floxcap/fly2040/pcb/usb_programmer/3DSteps/2-84952-4.step

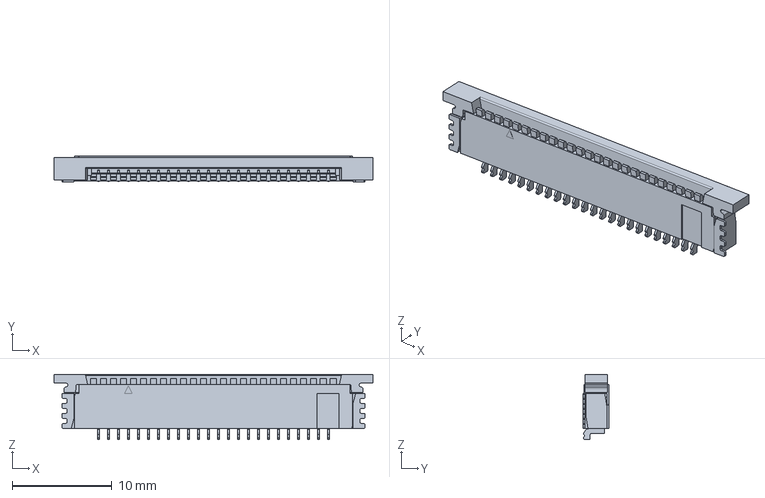
[picture p23: CAD file, 2023-07-07]
pcb/usb_programmer/3DSteps/2-84952-4.step
31.9 x 2.56 x 6.54 mm
