floxcap/fly2040/pcb/usb_programmer/3DSteps/S2B-PH-SM4-TB(LF)(SN)--3DModel-STEP-56544.STEP

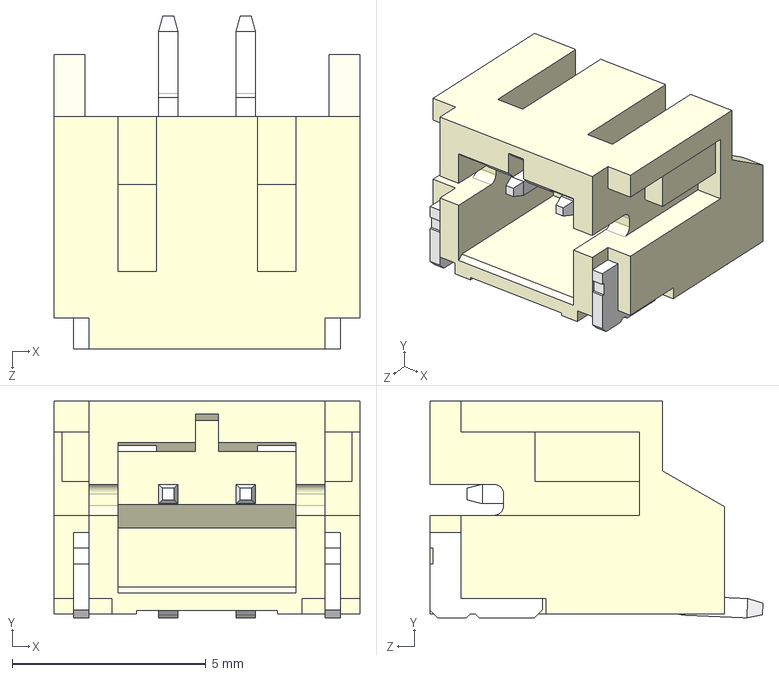
[picture p24: CAD file, 2023-07-07]
pcb/usb_programmer/3DSteps/S2B-PH-SM4-TB(LF)(SN)--3DModel-STEP-56544.STEP
7.90 x 5.60 x 8.60 mm
