floxcap/fly2040/pcb/usb_programmer/3DSteps/KMR621NG LFS.step

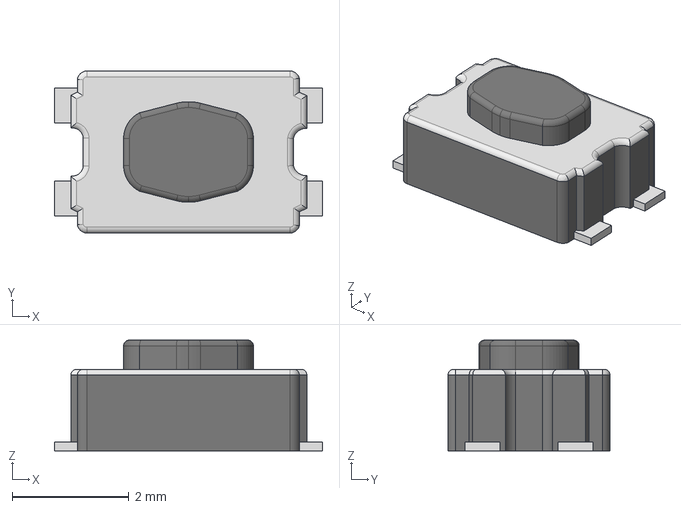
[picture p25: CAD file, 2023-07-07]
pcb/usb_programmer/3DSteps/KMR621NG LFS.step
4.60 x 2.78 x 1.90 mm
