floxcap/fly2040/pcb/usb_programmer/3DSteps/WLCSP6_1P48X0P98_ONS.step

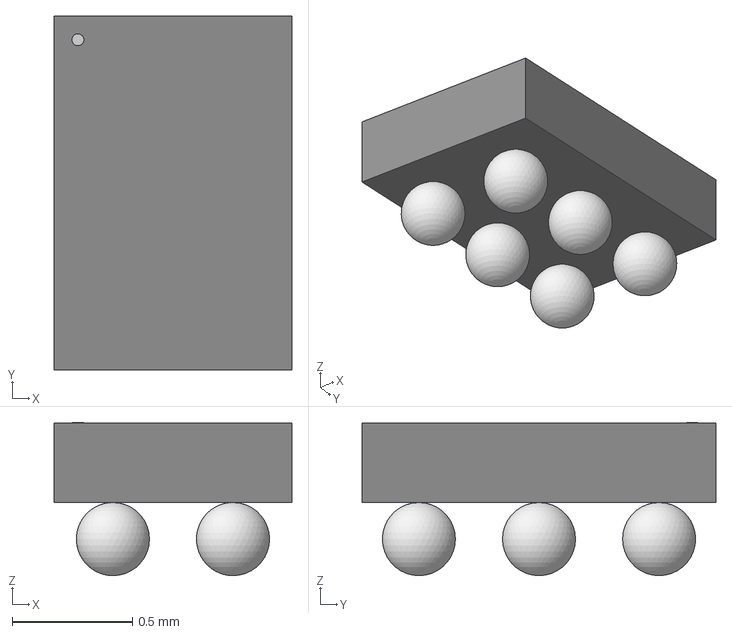
[picture p26: CAD file, 2023-07-07]
pcb/usb_programmer/3DSteps/WLCSP6_1P48X0P98_ONS.step
0.99 x 1.47 x 0.638 mm
