floxcap/fly2040/app/manager/src/pulse_tab.hpp

#pragma once

#include <borealis.hpp>

class PulseTab : public brls::Box
{
  public:
    PulseTab();

    static brls::View* create();

  private:
    BRLS_BIND(brls::Slider, brightness, "brightness");
    BRLS_BIND(brls::Slider, speed, "speed");
    BRLS_BIND(brls::Slider, hue, "hue");

    BRLS_BIND(brls::Label, brightness_lbl, "brightness_lbl");
    BRLS_BIND(brls::Label, speed_lbl, "speed_lbl");
    BRLS_BIND(brls::Label, hue_lbl, "hue_lbl");
};
